TheOneTheProdigy/DCC-Locomotive-Throttle/config_buttons_example.h

#define DEVICE_NAME "Loco Throttle"

// ********************************************************************************************

// false = Counter clockwise  true = clockwise
#define ENCODER_ROTATION_CLOCKWISE_IS_INCREASE_SPEED                     true

// Define what the rotary encoder button does.   (Pushing down on the knob)
// By default it will stop the loco if moving, then a second push will change the direction.
// Uncomment and change the action if you wish it to do something else.
// See static.h or README.md for details on the allowed functions.

// #define ENCODER_BUTTON_ACTION SPEED_STOP_THEN_TOGGLE_DIRECTION 

// true = if the locos(s) are stationary, clicking the encoder button will toggle the direction
// this only takes effect if the ENCODER_BUTTON_ACTION (above) is set to SPEED_STOP_THEN_TOGGLE_DIRECTION

#define TOGGLE_DIRECTION_ON_ENCODER_BUTTON_PRESSED_WHEN_STATIONARY         true

// ********************************************************************************************

// define what each button will do as direct press (not in a menu)   * and # cannot be remapped
// see static.h or README.md for details on the allowed functions

#define CHOSEN_KEYPAD_0_FUNCTION     FUNCTION_0
#define CHOSEN_KEYPAD_1_FUNCTION     FUNCTION_1
#define CHOSEN_KEYPAD_2_FUNCTION     FUNCTION_2
#define CHOSEN_KEYPAD_3_FUNCTION     FUNCTION_3
#define CHOSEN_KEYPAD_4_FUNCTION     FUNCTION_4
#define CHOSEN_KEYPAD_5_FUNCTION     FUNCTION_5
#define CHOSEN_KEYPAD_6_FUNCTION     FUNCTION_6
#define CHOSEN_KEYPAD_7_FUNCTION     FUNCTION_7
#define CHOSEN_KEYPAD_8_FUNCTION     FUNCTION_8
#define CHOSEN_KEYPAD_9_FUNCTION     FUNCTION_9

// text that will appear when you press #
// if you rearrange the items above, modify this text to suit    * and # cannot be remapped here

#define CHOSEN_KEYPAD_0_DISPLAY_NAME     "0 Lights"
#define CHOSEN_KEYPAD_1_DISPLAY_NAME     "1 Bell"
#define CHOSEN_KEYPAD_2_DISPLAY_NAME     "2 Horn"
#define CHOSEN_KEYPAD_3_DISPLAY_NAME     "3 F3"
#define CHOSEN_KEYPAD_4_DISPLAY_NAME     "4 F4"
#define CHOSEN_KEYPAD_5_DISPLAY_NAME     "5 F5"
#define CHOSEN_KEYPAD_6_DISPLAY_NAME     "6 Brakes"
#define CHOSEN_KEYPAD_7_DISPLAY_NAME     "7 F7"
#define CHOSEN_KEYPAD_8_DISPLAY_NAME     "8 F8"
#define CHOSEN_KEYPAD_9_DISPLAY_NAME     "9 F9"

// by default, # will show the list above. 
// if you change the following line to true, it will take you to the Loco Function Labels screen directly

#define HASH_SHOWS_FUNCTIONS_INSTEAD_OF_KEY_DEFS         false

// ********************************************************************************************

// define the number of throttles that you want.
// to use multiple throttles, one of the keys or buttons will need to be defined as NEXT_THROTTLE.  (keypad 5 is by default)
// Maximum supported by the WiThrottleProtocol is 6

// #define MAX_THROTTLES                 2          // uncomment and increase the number if you always need more that two throttles

// ********************************************************************************************

// DCC Addresses below or equal to this number will be treated as short addresses.  
// DCC++EX, NCE, Digitrax use 127, Lenz use 99

#define SHORT_DCC_ADDESS_LIMIT         127  

// speed increase for each click of the encoder 

#define SPEED_STEP                       2
#define SPEED_STEP_MULTIPLIER            3          // for 'fast' speed steps

// Additional multiplier.  If the multiplier is enabled from the menu, each rotation of the encoder becomes the speedStep * the AdditionalMultiplier

#define SPEED_STEP_ADDITIONAL_MULTIPLIER 2

// by default, the speed will be displayed as the the DCC speed (0-126)
// IMPORTANT: only one should be enabled.  If DISPLAY_SPEED_AS_PERCENT is enabled it will take presidence over DISPLAY_SPEED_AS_0_TO_28
// Note: there will be rounding errors!

// uncomment this line to display the speeds a percentage.
#define DISPLAY_SPEED_AS_PERCENT         true
// uncomment this line to display the speeds as 0-28.
// #define DISPLAY_SPEED_AS_0_TO_28         true

// ********************************************************************************************
// DCC functions in consists
#define CONSIST_FUNCTION_FOLLOW_F0                  CONSIST_ALL_LOCOS            // lights
#define CONSIST_FUNCTION_FOLLOW_F1                  CONSIST_LEAD_LOCO            // bell
#define CONSIST_FUNCTION_FOLLOW_F2                  CONSIST_LEAD_LOCO            // horn
#define CONSIST_FUNCTION_FOLLOW_F6                  CONSIST_ALL_LOCOS            // brakes
#define CONSIST_FUNCTION_FOLLOW_OTHER_FUNCTIONS     CONSIST_LEAD_LOCO

// ********************************************************************************************

// define what each of the optional additional buttons will do
// see static.h or README.md for details on the allowed functions
// all must be included, just set the ones you don't need to FUNCTION_NULL
// the button numbers relate to the GPIO pins 5,15,25,26,27,32,33

#define CHOSEN_ADDITIONAL_BUTTON_0_FUNCTION     FUNCTION_NULL   // GPIO 5
#define CHOSEN_ADDITIONAL_BUTTON_1_FUNCTION     FUNCTION_NULL   // GPIO 15
#define CHOSEN_ADDITIONAL_BUTTON_2_FUNCTION     FUNCTION_NULL   // GPIO 25
#define CHOSEN_ADDITIONAL_BUTTON_3_FUNCTION     FUNCTION_NULL   // GPIO 26
#define CHOSEN_ADDITIONAL_BUTTON_4_FUNCTION     FUNCTION_NULL   // GPIO 27
#define CHOSEN_ADDITIONAL_BUTTON_5_FUNCTION     FUNCTION_NULL   // GPIO 32
#define CHOSEN_ADDITIONAL_BUTTON_6_FUNCTION     FUNCTION_NULL   // GPIO 33

#define ADDITIONAL_BUTTON_DEBOUNCE_DELAY        50           // increase if you find the buttons bounce. i.e. activate twice on a single press

// ********************************************************************************************

// uncomment and/or correct one (only) of the #define lines below if you need to override the default .9 inch oLED dispaly settings 
//
// Please select a constructor line for below depending on your display
// U8g2 Constructor List (Frame Buffer)
// The complete list is available here: https://github.com/olikraus/u8g2/wiki/u8g2setupcpp
// Please update the pin numbers according to your setup. Use U8X8_PIN_NONE if the reset pin is not connected

// this is one of the common .9 inch OLED displays and is included by default

// #define OLED_TYPE U8G2_SSD1306_128X64_NONAME_F_HW_I2C u8g2(U8G2_R0, /* reset=*/ U8X8_PIN_NONE, /* clock=*/ 22, /* data=*/ 23);

// this is one of the common 1.3 inch OLED displays

#define OLED_TYPE U8G2_SH1106_128X64_NONAME_F_HW_I2C u8g2(U8G2_R0, /* reset=*/ U8X8_PIN_NONE, /* clock=*/ 22, /* data=*/ 23);

// *******************************************************************************************************************
// Debugging

// DCC LocomotiveThrottle console debug messages are ENABLED by default
// to disable to console messages, set the following to  1    (i.e. 0 = on  1 = off)
#define DCCLOCOMOTIVETHROTTLEDEBUG    0

// WiThrottleProtocol console debug messages are DISABLED by default
// to enable console messages, set the follow to  0    (i.e. 0 = on  1 = off)
#define WITHROTTLE_PROTOCOL_DEBUG   1
